jfedor2/flatbox/hardware-rev2/extras/Flatbox-rev2-schematic.pdf

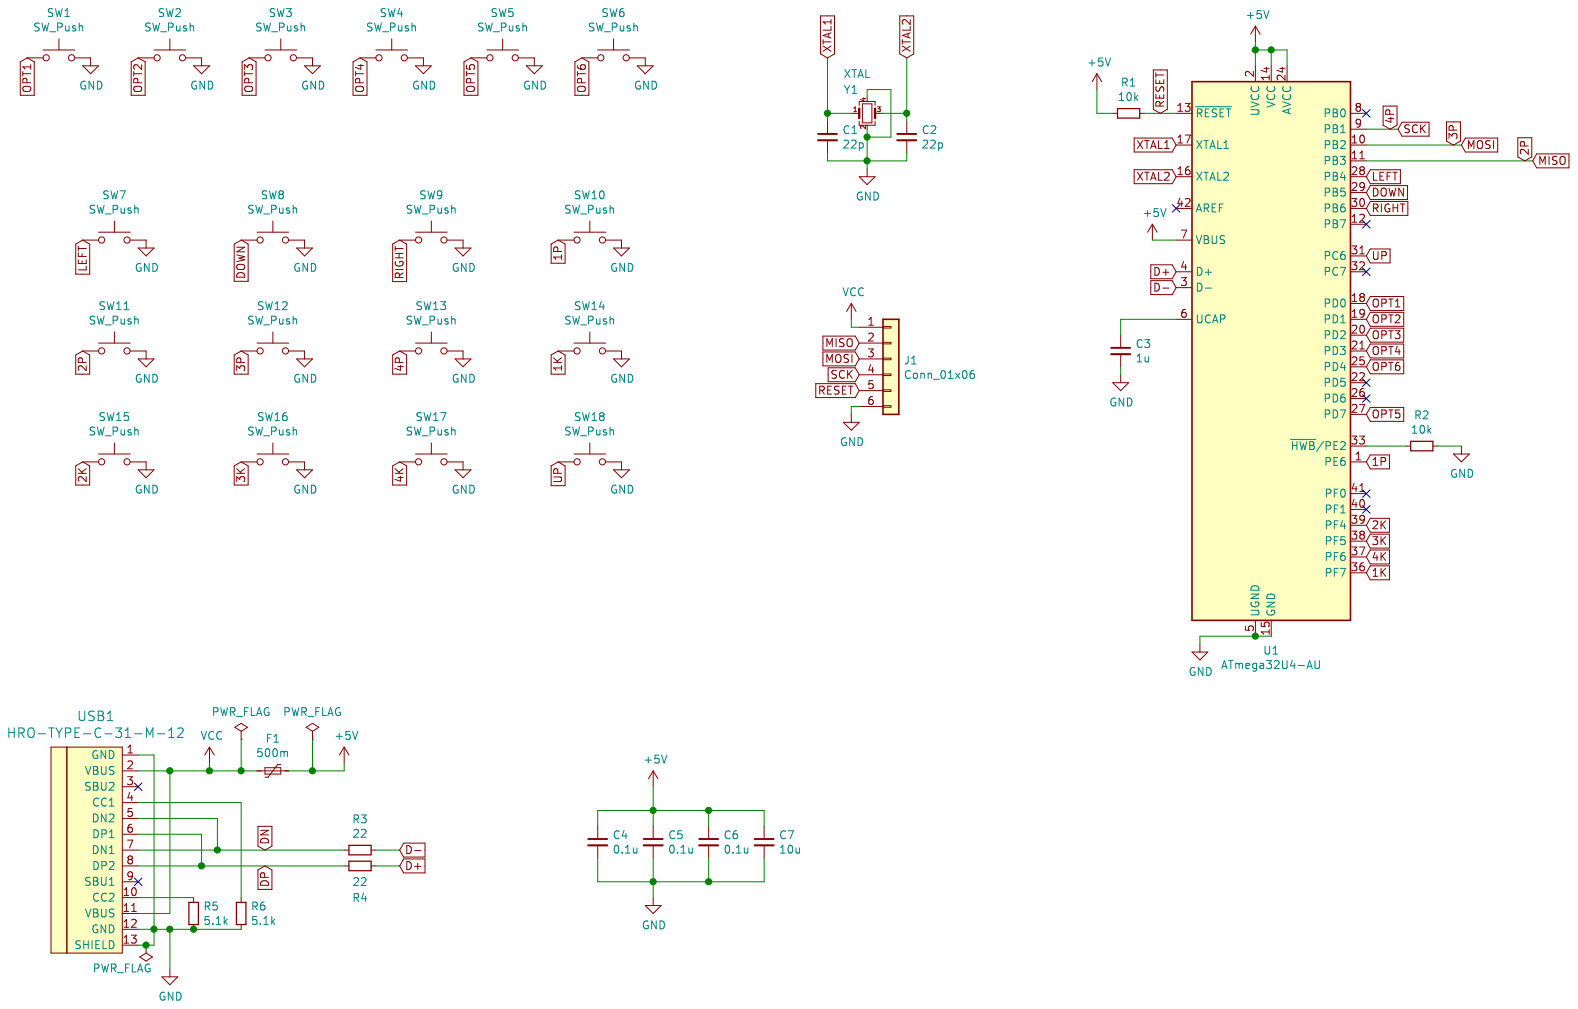
[picture p47: page 1]
