jfedor2/flatbox/firmware-ch552/src/config.h

#pragma once

// USB device descriptor
#define USB_VENDOR_ID 0x0F0D
#define USB_PRODUCT_ID 0x00C1
#define USB_DEVICE_VERSION  0x0100    // v1.0 (BCD-format)

// USB configuration descriptor
#define USB_MAX_POWER_mA    50        // max power in mA 

// USB descriptor strings
#define MANUFACTURER_STR    'C','H','5','5','2'
#define PRODUCT_STR         'F','l','a','t','b','o','x',' ','r','e','v','6'
