jfedor2/flatbox/firmware-ch552/src/delay.c

// ===================================================================================
// Delay Functions for CH551, CH552 and CH554
// ===================================================================================

#include "delay.h"
#include "ch554.h"

// ===================================================================================
// Delay in Units of us
// ===================================================================================
void DLY_us(uint16_t n) {           // delay in us
  #ifdef F_CPU
    #if F_CPU <= 6000000
      n >>= 2;
    #endif
    #if F_CPU <= 3000000
      n >>= 2;
    #endif
    #if F_CPU <= 750000
      n >>= 4;
    #endif
  #endif

  while(n) {                        // total = 12~13 Fsys cycles, 1uS @Fsys=12MHz
    SAFE_MOD++;                     // 2 Fsys cycles, for higher Fsys, add operation here
    #ifdef F_CPU
      #if F_CPU >= 14000000
        SAFE_MOD++;
      #endif
      #if F_CPU >= 16000000
        SAFE_MOD++;
      #endif
      #if F_CPU >= 18000000
        SAFE_MOD++;
      #endif
      #if F_CPU >= 20000000
        SAFE_MOD++;
      #endif
      #if F_CPU >= 22000000
        SAFE_MOD++;
      #endif
      #if F_CPU >= 24000000
        SAFE_MOD++;
      #endif
      #if F_CPU >= 26000000
        SAFE_MOD++;
      #endif
      #if F_CPU >= 28000000
        SAFE_MOD++;
      #endif
      #if F_CPU >= 30000000
        SAFE_MOD++;
      #endif
      #if F_CPU >= 32000000
		    SAFE_MOD++;
      #endif
    #endif
		n--;
  }
}

// ===================================================================================
// Delay in Units of ms
// ===================================================================================
void DLY_ms(uint16_t n) {           // delay in ms
  while(n) {
    DLY_us(1000);
    n--;
  }
}

// ===================================================================================
// Delay 20+4*(n-1) Clock Cycles
// ===================================================================================
#pragma callee_saves _delay_more_cycles
void _delay_more_cycles (uint8_t n) __naked {
  n;              // stop unreferenced arg warning
  __asm
    .even         ; make predictable cycles for jumps
    push ar7      ; 2 cycles
    mov  r7, dpl  ; 2 cycles
    djnz r7, .+0  ; 2/4 cycles
    pop  ar7      ; 2 cycles
    ret           ; 4|5 cycles
  __endasm;
}
